simonyiszk/SEM_ProjektoroSCH/Schematic & Layout/Output/projektorosch.jpg

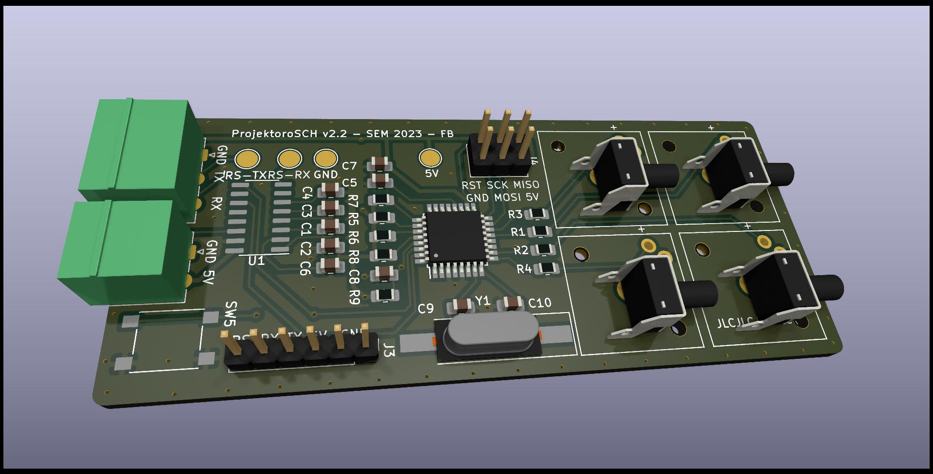
Schematic & Layout/Output/projektorosch.jpg
